bishboria/ErgoDox/ErgoDox Acrylic Case/ErgoDOX Acrylic Case - Designed by Litster/with Wrist Rest/Left/ErgoDOX Case Layer 1 Top - Left.dxf

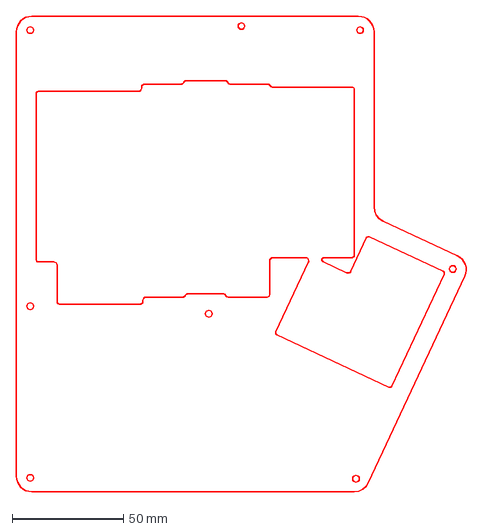
[picture p15: CAD file, 2013-07-07]
ErgoDox Acrylic Case/ErgoDOX Acrylic Case - Designed by Litster/with Wrist Rest/Left/ErgoDOX Case Layer 1 Top - Left.dxf
202.8 x 214.1 mm
