bishboria/ErgoDox/ErgoDox Acrylic Case/ErgoDOX Acrylic Case - Designed by Litster/with Wrist Rest/Right/ErgoDOX Wrist Rest Case Layer 3 Plate - Right.dxf

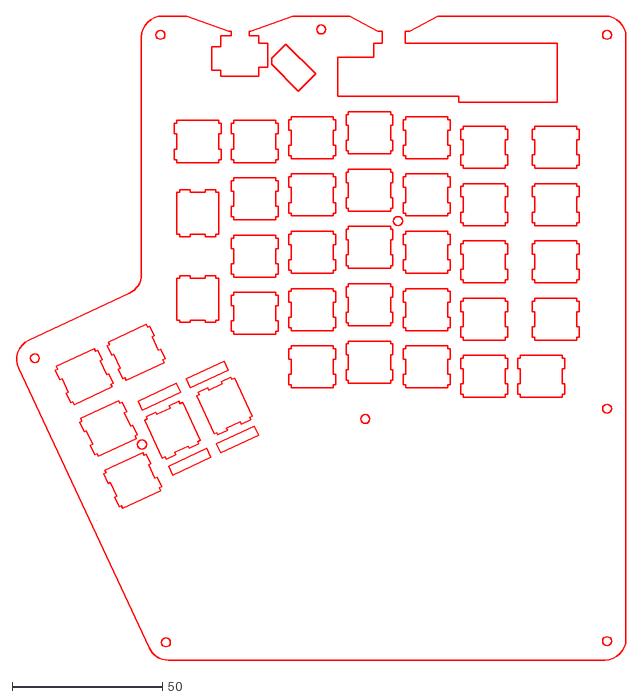
[picture p16: CAD file, 2013-07-07]
ErgoDox Acrylic Case/ErgoDOX Acrylic Case - Designed by Litster/with Wrist Rest/Right/ErgoDOX Wrist Rest Case Layer 3 Plate - Right.dxf
202.8 x 214.1
