bishboria/ErgoDox/ErgoDox Acrylic Case/ErgoDOX Acrylic Case - Designed by Litster/Standard/Right/ErgoDOX Case Layer 5 Bottom - Right.dxf

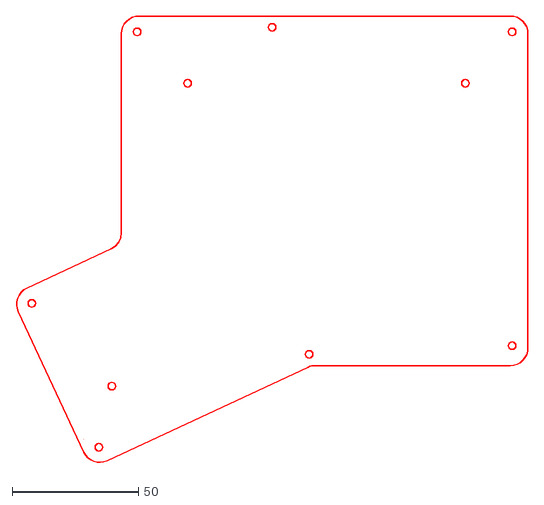
[picture p18: CAD file, 2013-07-07]
ErgoDox Acrylic Case/ErgoDOX Acrylic Case - Designed by Litster/Standard/Right/ErgoDOX Case Layer 5 Bottom - Right.dxf
202.8 x 177.8
