bishboria/ErgoDox/ErgoDox Acrylic Case/ErgoDOX Acrylic Case - Designed by Litster/with Wrist Rest/Left/ErgoDOX Case Layer 4 Spacer - Left.dxf

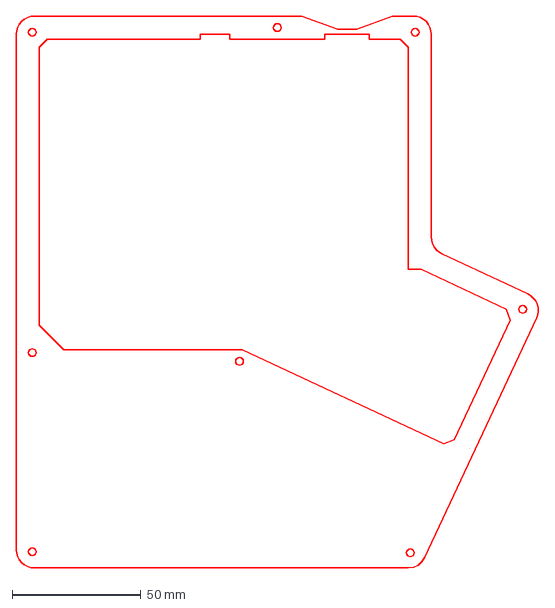
[picture p19: CAD file, 2013-07-07]
ErgoDox Acrylic Case/ErgoDOX Acrylic Case - Designed by Litster/with Wrist Rest/Left/ErgoDOX Case Layer 4 Spacer - Left.dxf
202.8 x 214.1 mm
