bishboria/ErgoDox/ErgoDox Acrylic Case/ErgoDOX Acrylic Case - Designed by Litster/with Wrist Rest/Right/ErgoDOX Wrist Rest Case Layer 5 Bottom - Right.dxf

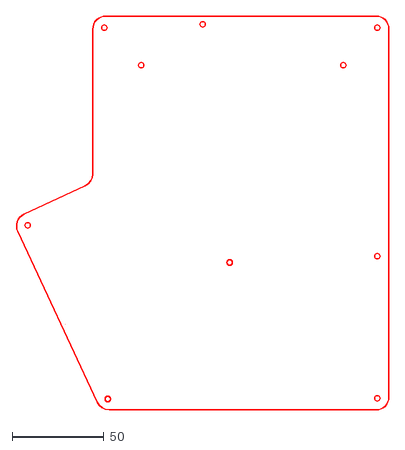
[picture p20: CAD file, 2013-07-07]
ErgoDox Acrylic Case/ErgoDOX Acrylic Case - Designed by Litster/with Wrist Rest/Right/ErgoDOX Wrist Rest Case Layer 5 Bottom - Right.dxf
202.8 x 214.1
