bishboria/ErgoDox/ErgoDox Acrylic Case/ErgoDOX Acrylic Case - Designed by Litster/with Wrist Rest/Left/test cut.dxf

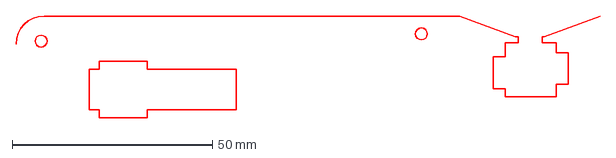
[picture p21: CAD file, 2013-07-07]
ErgoDox Acrylic Case/ErgoDOX Acrylic Case - Designed by Litster/with Wrist Rest/Left/test cut.dxf
146.0 x 25.5 mm
